julia-laine-11/grad-cap/photos/Screenshot from 2026-01-12 10-53-48.png

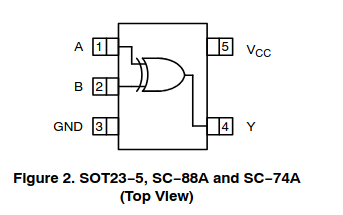
photos/Screenshot from 2026-01-12 10-53-48.png
