julia-laine-11/grad-cap/photos/Screenshot from 2026-01-12 10-54-43.png

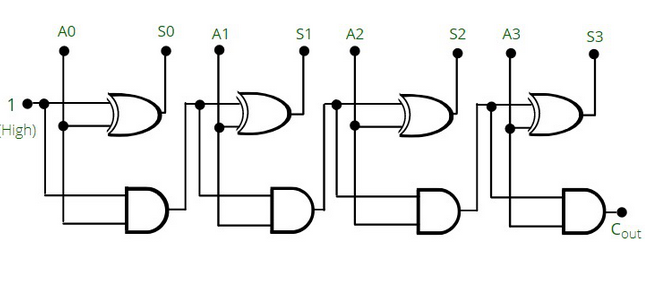
photos/Screenshot from 2026-01-12 10-54-43.png
