julia-laine-11/grad-cap/photos/Screenshot from 2026-01-22 11-57-02.png

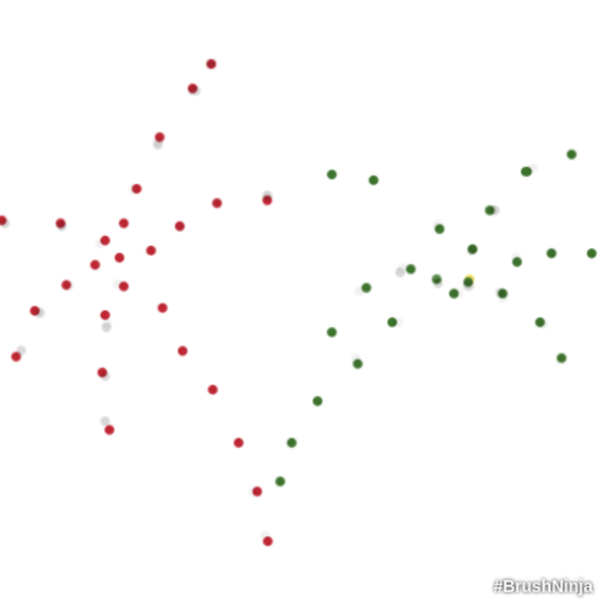
photos/Screenshot from 2026-01-22 11-57-02.png
