julia-laine-11/grad-cap/photos/Screenshot from 2026-01-22 17-45-35.png

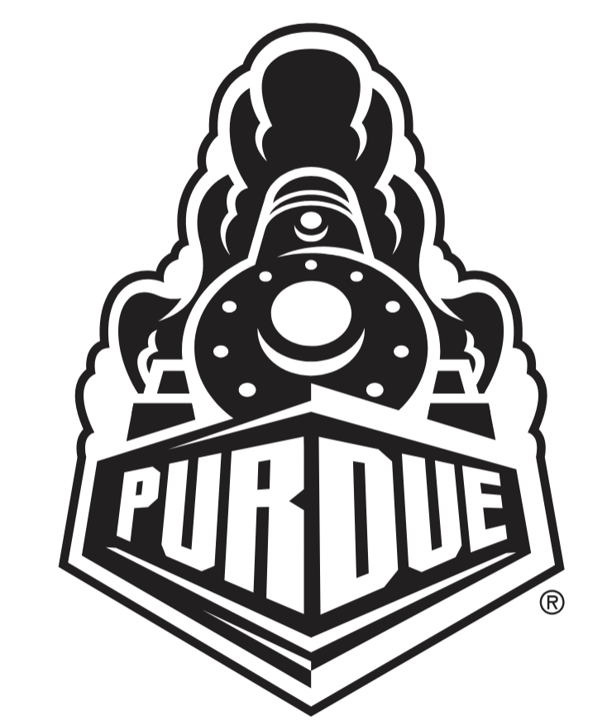
photos/Screenshot from 2026-01-22 17-45-35.png
