julia-laine-11/grad-cap/photos/Screenshot from 2026-01-22 17-49-14.png

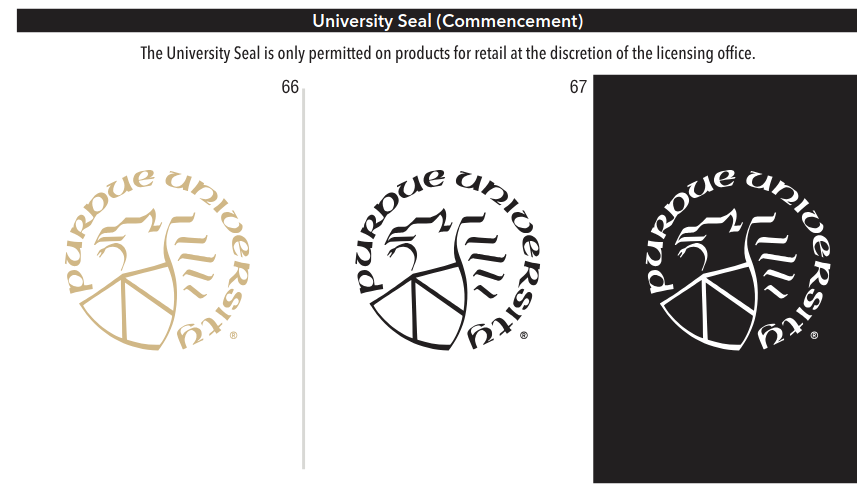
photos/Screenshot from 2026-01-22 17-49-14.png
